soa-boya-parking/proyecto/Sistema-Embebido/DiagramasFinal/Diagrama de Estados.png

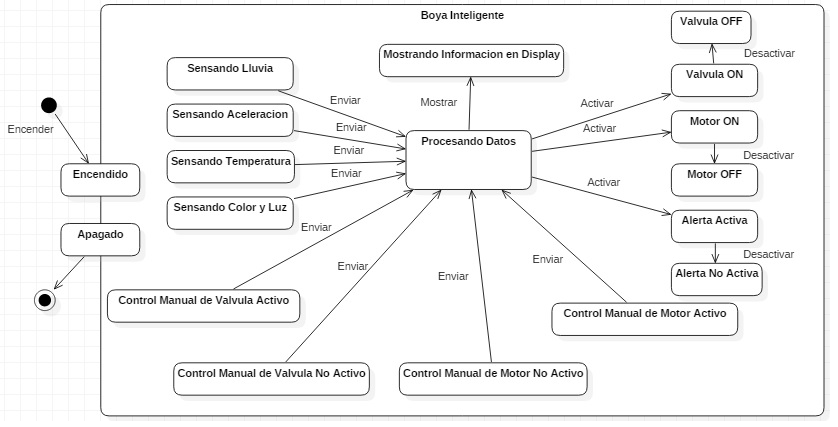
Sistema-Embebido/DiagramasFinal/Diagrama de Estados.png
