soa-boya-parking/proyecto/Sistema-Embebido/DiagramasFinal/Diagrama en Bloques.png

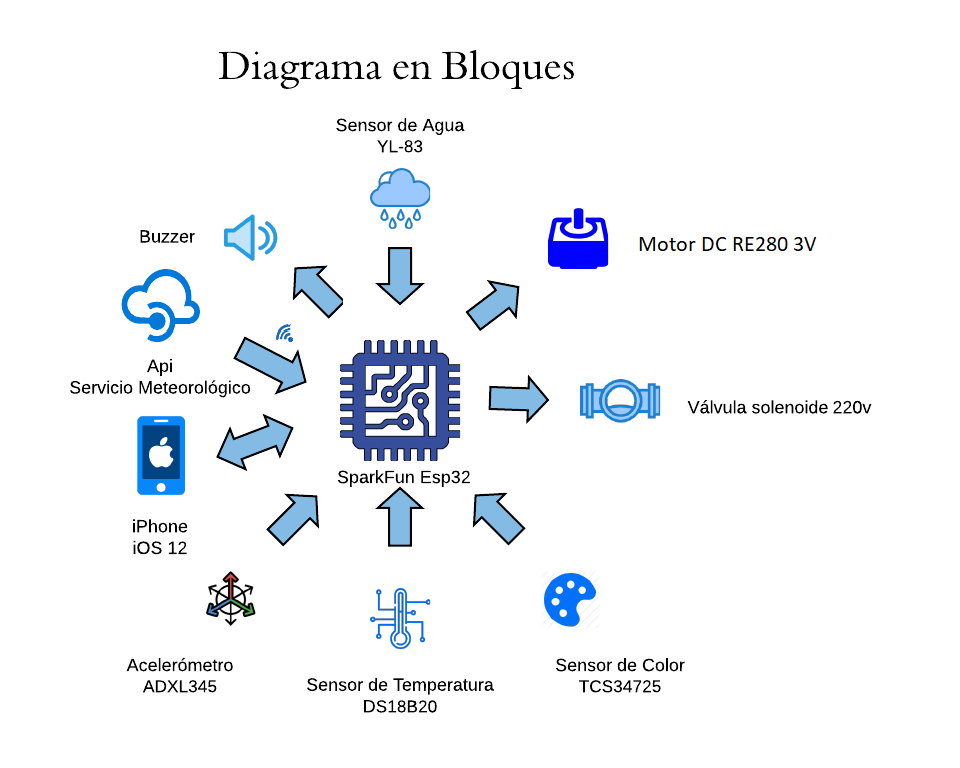
Sistema-Embebido/DiagramasFinal/Diagrama en Bloques.png
