soa-boya-parking/proyecto/Sistema-Embebido/DiagramasFinal/Diagrama Funcional.png

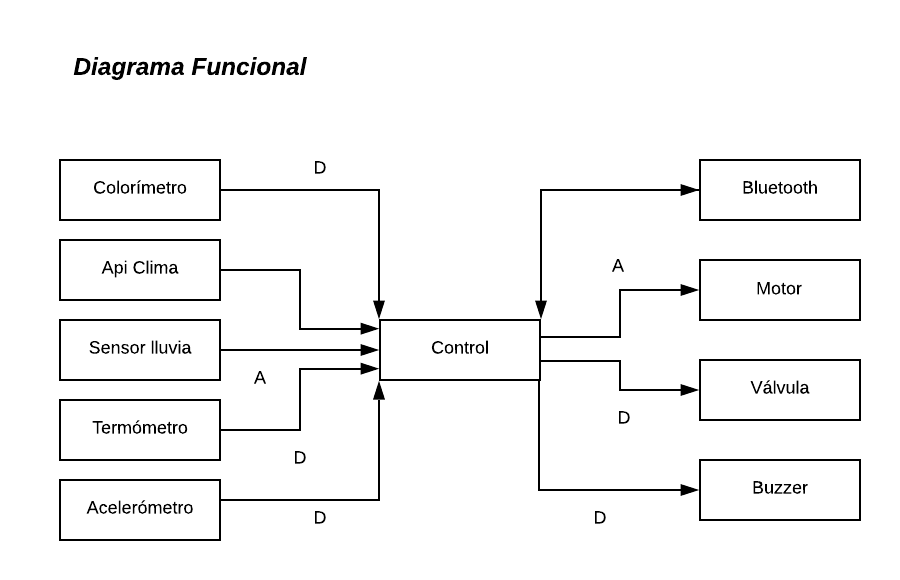
Sistema-Embebido/DiagramasFinal/Diagrama Funcional.png
