soa-boya-parking/proyecto/Sistema-Embebido/DiagramasFinal/Diagrama Logico.png

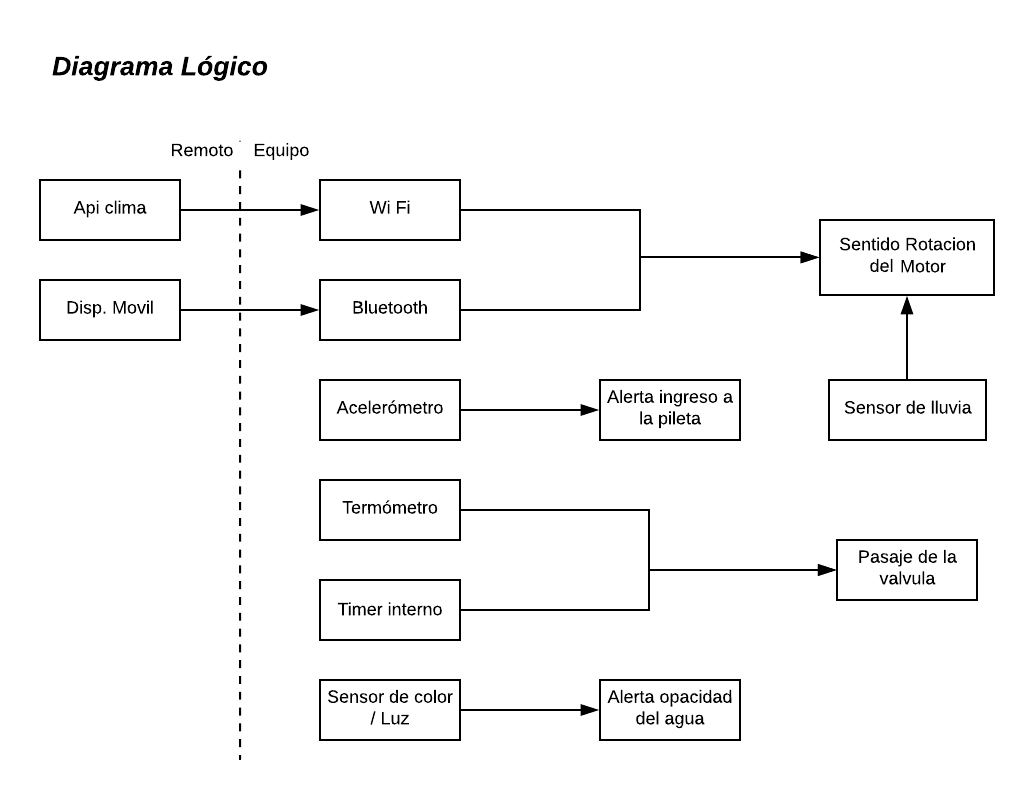
Sistema-Embebido/DiagramasFinal/Diagrama Logico.png
